keenanjohnson/Power-Line/Testing/Hardware test/WebServer/WebServer.ino

/*--------------------------------------------------------------
  Program:      eth_websrv_SD_Ajax_XML

  Description:  Arduino web server that serves up a web page
                that displays the status of two switches and
                one analog input.
                The web page is stored on the SD card.
                The web page contains JavaScript code that uses
                Ajax and XML to get the states of the switches
                and value of the analog input.
  
  Hardware:     Arduino Uno and official Arduino Ethernet
                shield. Should work with other Arduinos and
                compatible Ethernet shields.
                2Gb micro SD card formatted FAT16.
                Push button switches interfaced to pin 7 and 8
                of the Arduino. Potentiometer interfaced to A2
                analog input.
                
  Software:     Developed using Arduino 1.0.5 software
                Should be compatible with Arduino 1.0 +
                SD card contains web page called index.htm
  
  References:   - WebServer example by David A. Mellis and 
                  modified by Tom Igoe
                - SD card examples by David A. Mellis and
                  Tom Igoe
                - Ethernet library documentation:
                  http://arduino.cc/en/Reference/Ethernet
                - SD Card library documentation:
                  http://arduino.cc/en/Reference/SD

  Date:         27 March 2013
  Modified:     17 June 2013
                - removed the use of the String class
 
  Author:       W.A. Smith, http://startingelectronics.com
--------------------------------------------------------------*/

#include <SPI.h>
#include <Ethernet.h>
#include <SD.h>

// size of buffer used to capture HTTP requests
#define REQ_BUF_SZ   50

// MAC address from Ethernet shield sticker under board
byte mac[] = { 0xDE, 0xAD, 0xBE, 0xEF, 0xFE, 0xED };
IPAddress ip(192,168,1,23); // IP address, may need to change depending on network
EthernetServer server(80);  // create a server at port 80
File webFile;               // the web page file on the SD card
char HTTP_req[REQ_BUF_SZ] = {0}; // buffered HTTP request stored as null terminated string
char req_index = 0;              // index into HTTP_req buffer

void setup()
{
    // seed random number
    randomSeed(analogRead(0));

    // disable Ethernet chip
    pinMode(10, OUTPUT);
    digitalWrite(10, HIGH);
    
    Serial.begin(9600);       // for debugging
    
    // initialize SD card
    Serial.println("Initializing SD card...");
    if (!SD.begin(4)) {
        Serial.println("ERROR - SD card initialization failed!");
        return;    // init failed
    }
    Serial.println("SUCCESS - SD card initialized.");
    // check for index.htm file
    if (!SD.exists("index.htm")) {
        Serial.println("ERROR - Can't find index.htm file!");
        return;  // can't find index file
    }
    Serial.println("SUCCESS - Found index.htm file.");
    pinMode(7, INPUT);        // switch is attached to Arduino pin 7
    pinMode(8, INPUT);        // switch is attached to Arduino pin 8
    
    Ethernet.begin(mac, ip);  // initialize Ethernet device
    server.begin();           // start to listen for clients
}

void loop()
{
    EthernetClient client = server.available();  // try to get client

    if (client) {  // got client?
        boolean currentLineIsBlank = true;
        while (client.connected()) {
            if (client.available()) {   // client data available to read
                char c = client.read(); // read 1 byte (character) from client
                // buffer first part of HTTP request in HTTP_req array (string)
                // leave last element in array as 0 to null terminate string (REQ_BUF_SZ - 1)
                if (req_index < (REQ_BUF_SZ - 1)) {
                    HTTP_req[req_index] = c;          // save HTTP request character
                    req_index++;
                }
                // last line of client request is blank and ends with \n
                // respond to client only after last line received
                if (c == '\n' && currentLineIsBlank) {
                    // send a standard http response header
                    client.println("HTTP/1.1 200 OK");
                    // remainder of header follows below, depending on if
                    // web page or XML page is requested
                    // Ajax request - send XML file
                    if (StrContains(HTTP_req, "ajax_inputs")) {
                        // send rest of HTTP header
                        client.println("Content-Type: text/xml");
                        client.println("Connection: keep-alive");
                        client.println();
                        // send XML file containing input states
                        XML_response(client);
                    }
                    else {  // web page request
                        // send rest of HTTP header
                        client.println("Content-Type: text/html");
                        client.println("Connection: keep-alive");
                        client.println();
                        // send web page
                        webFile = SD.open("index.htm");        // open web page file
                        if (webFile) {
                            while(webFile.available()) {
                                client.write(webFile.read()); // send web page to client
                            }
                            webFile.close();
                        }
                    }
                    // display received HTTP request on serial port
                    Serial.print(HTTP_req);
                    // reset buffer index and all buffer elements to 0
                    req_index = 0;
                    StrClear(HTTP_req, REQ_BUF_SZ);
                    break;
                }
                // every line of text received from the client ends with \r\n
                if (c == '\n') {
                    // last character on line of received text
                    // starting new line with next character read
                    currentLineIsBlank = true;
                } 
                else if (c != '\r') {
                    // a text character was received from client
                    currentLineIsBlank = false;
                }
            } // end if (client.available())
        } // end while (client.connected())
        delay(1);      // give the web browser time to receive the data
        client.stop(); // close the connection
    } // end if (client)
}

// send the XML file with switch statuses and analog value
void XML_response(EthernetClient cl)
{
    int analog_val;
    
    cl.print("<?xml version = \"1.0\" ?>");
    cl.print("<inputs>");
    // light count
    cl.print("<count>");
    cl.print(3);
    cl.print("</count>");
    // button 1, pin 7
    cl.print("<light1>");
    if (digitalRead(7)) {
        cl.print("ON");
    }
    else {
        cl.print("OFF");
    }
    cl.print("</light1>");
    // button 2, pin 8
    cl.print("<light2>");
    if (digitalRead(8)) {
        cl.print("ON");
    }
    else {
        cl.print("OFF");
    }
    cl.print("</light2>");
    // button 3, pin 6
    cl.print("<light3>");
    if (digitalRead(6)) {
        cl.print("ON");
    }
    else {
        cl.print("OFF");
    }
    cl.print("</light3>");
    
    // read analog pin A2
    analog_val = analogRead(2);
    cl.print("<analog1>");
    cl.print(analog_val);
    cl.print("</analog1>");
    cl.print("</inputs>");
}

// sets every element of str to 0 (clears array)
void StrClear(char *str, char length)
{
    for (int i = 0; i < length; i++) {
        str[i] = 0;
    }
}

// searches for the string sfind in the string str
// returns 1 if string found
// returns 0 if string not found
char StrContains(char *str, char *sfind)
{
    char found = 0;
    char index = 0;
    char len;

    len = strlen(str);
    
    if (strlen(sfind) > len) {
        return 0;
    }
    while (index < len) {
        if (str[index] == sfind[found]) {
            found++;
            if (strlen(sfind) == found) {
                return 1;
            }
        }
        else {
            found = 0;
        }
        index++;
    }

    return 0;
}
